tomaskovacik/vwcdpic/vwcdpic/vwcdpic_v2_full_pcb.jpg

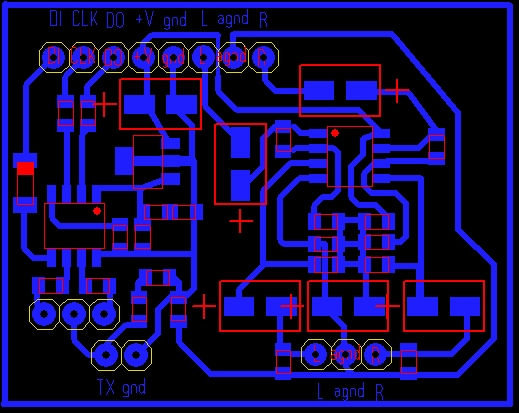
vwcdpic/vwcdpic_v2_full_pcb.jpg
