tomaskovacik/vwcdpic/vwcdpic/vwcdpic_v2_hard.jpg

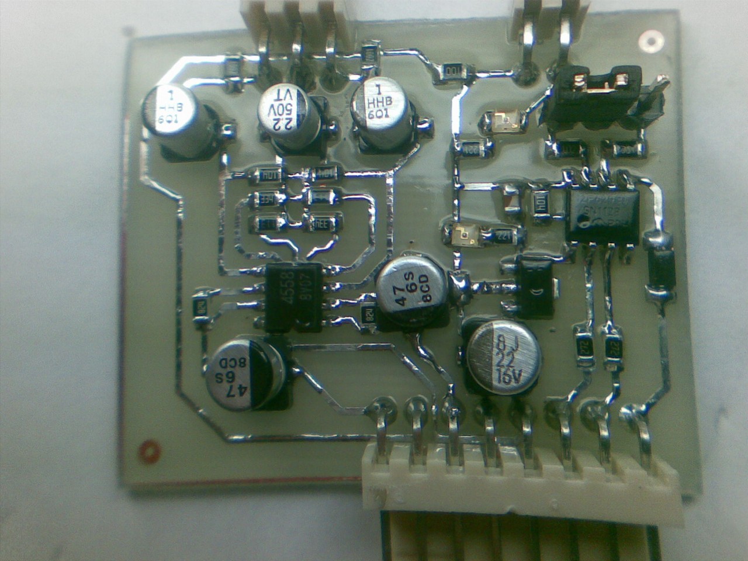
vwcdpic/vwcdpic_v2_hard.jpg
