tomaskovacik/vwcdpic/vwcdpic/powerctl-driver.png

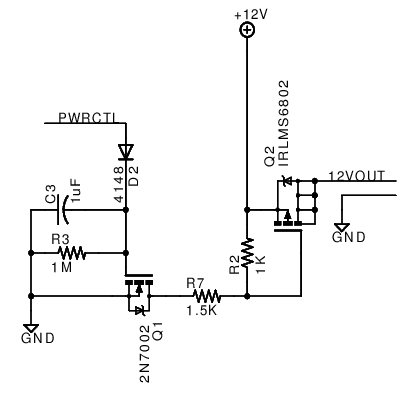
vwcdpic/powerctl-driver.png
