tomaskovacik/vwcdpic/vwcdpic/vwcdpic_v1.png

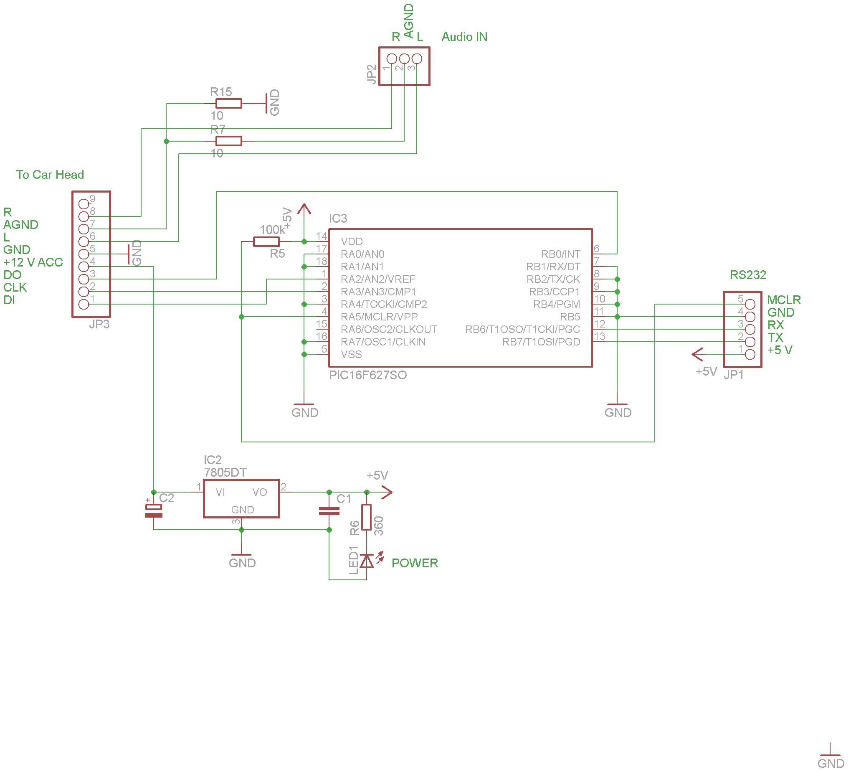
vwcdpic/vwcdpic_v1.png
