tomaskovacik/vwcdpic/vwcdpic/vwcdpic_v2.png

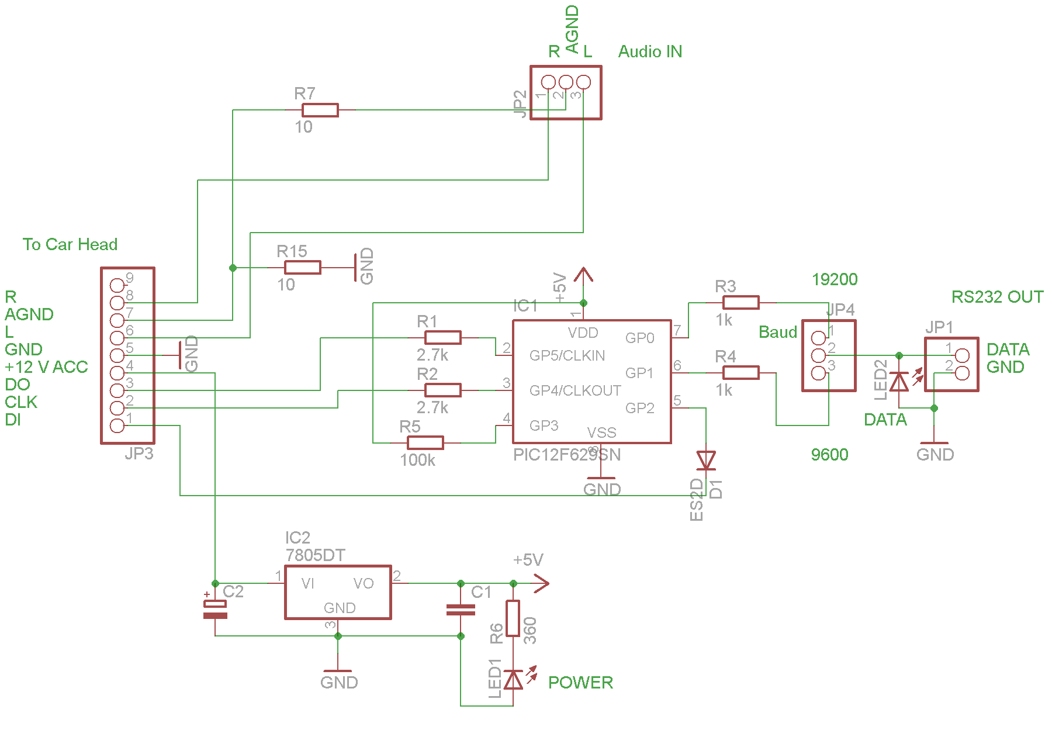
vwcdpic/vwcdpic_v2.png
