tomaskovacik/vwcdpic/vwcdpic/vwcdpic_v2_full.png

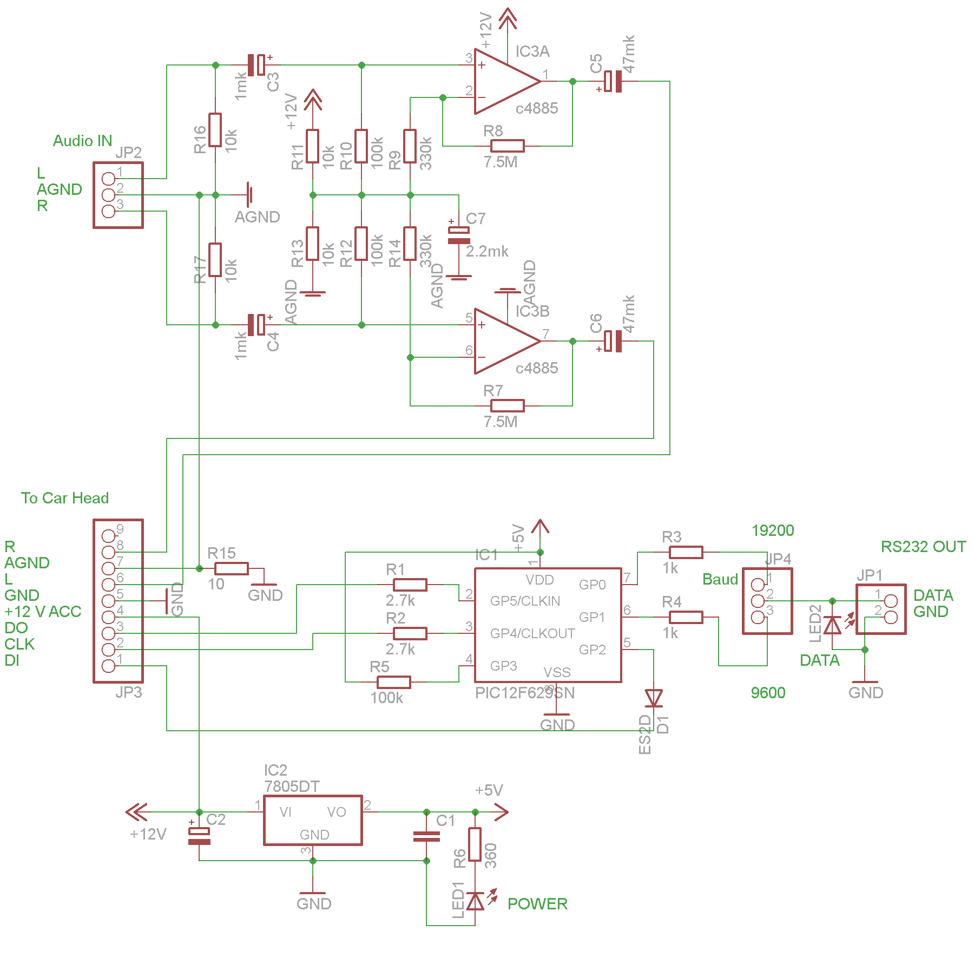
vwcdpic/vwcdpic_v2_full.png
