tomaskovacik/vwcdpic/vwcdpic_preamp.png

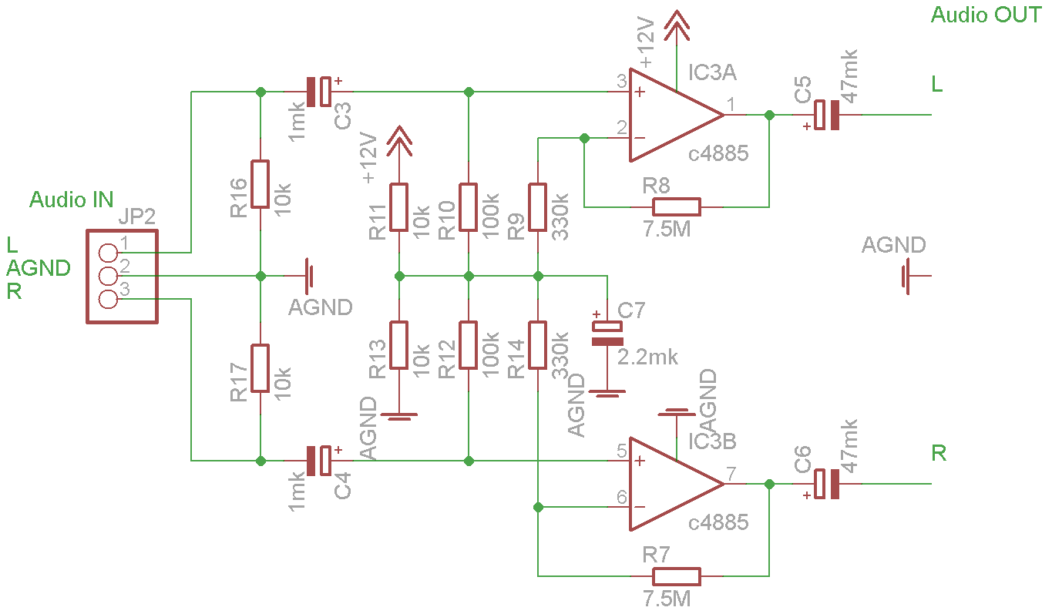
vwcdpic_preamp.png
