tomaskovacik/vwcdpic/vwcdpic_v3.png

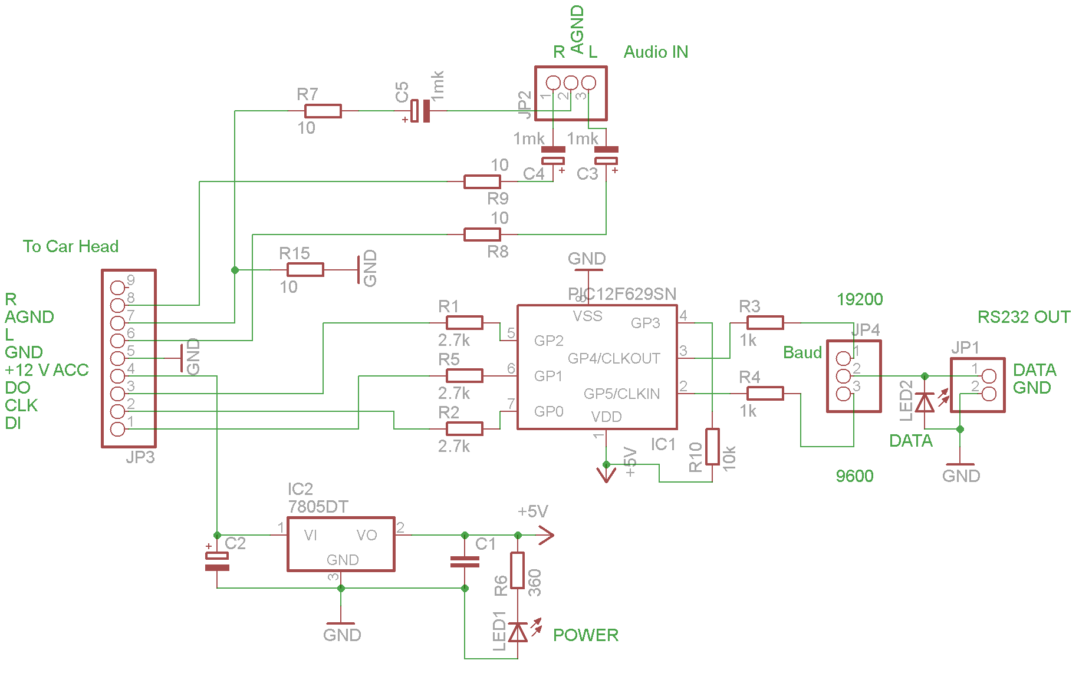
vwcdpic_v3.png
