tomaskovacik/vwcdpic/vwcdpic_v3_full.png

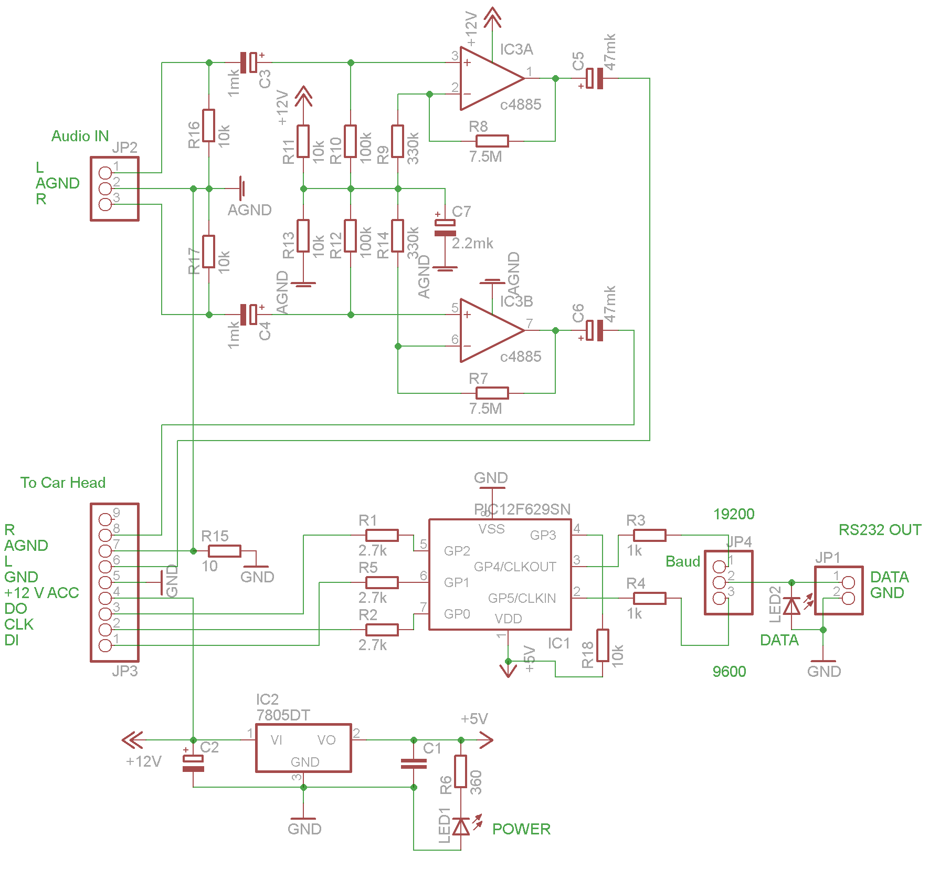
vwcdpic_v3_full.png
